flavio-muniz/controle-de-ambiente-IoT/schematics/esp32.kicad_sch

## KiCad design schematics/esp32.kicad_sch (2025-12-04)

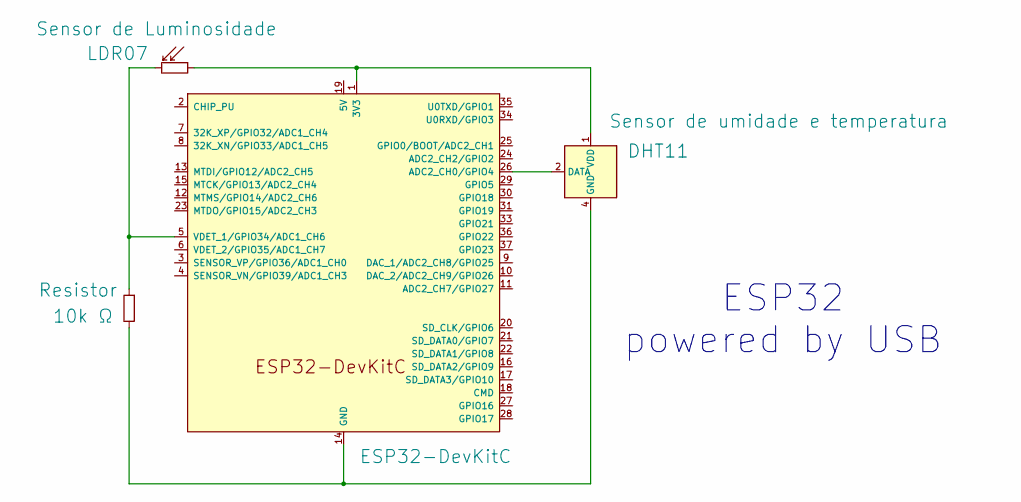
[picture p2: schematic esp32.kicad_sch]

Parts:
DHT11: Sensor de umidade e temperatura; Aosong_DHT11_5.5x12.0_P2.54mm
LDR07: Sensor de Luminosidade; R_LDR_5.1x4.3mm_P3.4mm_Vertical
Resistor: 10k Ω
U1: ESP32-DevKitC

Connections:
unnamed: DHT11.1 (VDD), LDR07.1, U1.1 (3V3)
unnamed: DHT11.2 (DATA), U1.26 (ADC2_CH0/GPIO4)
unnamed: DHT11.4 (GND), Resistor.1, U1.14 (GND), U1.32 (GND), U1.38 (GND)
unnamed: LDR07.2, Resistor.2, U1.5 (VDET_1/GPIO34/ADC1_CH6)

Notes on the sheet:
ESP32 powered by USB
